ebertmx/SCRAPPY-MK1/src/scrappy_gui.py

import PySimpleGUI as sg
from scrappy_server import *
from serial_reader import *
import traceback
import serial.tools.list_ports
import time

WIN_CLOSED = sg.WIN_CLOSED

STEP = 10

ZERO_POS = "0-position"
ONE_POS = "1-position"
TWO_POS = "2-position"
MAG_STAT = "magnet-status"

ZERO_MOTOR = 0
ONE_MOTOR = 1
TWO_MOTOR = 2

POS = 1
NEG = -1

cmd_list = ["P:0,-350,3000, 50, 30, 50", "P:500,-350,2800, 50, 50, 50","P:500,-550,2900, 50, 30, 30","M:1,0,0,0,0,0","P:-500,-200,2800, 50, 50, 50", "P:-500,-550,2900, 50, 30, 30",  "M:0,0,0,0,0,0","P:0,-350,3000, 50, 50, 50"] # just enter whatever commands you want in this list


class Window(sg.Window):

    def __init__(self):
        super(Window, self).__init__("SCRAPPY-MK1", layout, finalize=True, resizable=True)
        self.serial = None
        self.server = None


def move_0(args, window):
    pass


def move_1(args, window):
    pass


def move_2(args, window):
    pass


def calibrate(args, window):
    pass


def submit(args, window):
    pass


def test(args, window):
    count = 1
    for i in cmd_list:
        window.server.send_command(i)
        if count==1: 
            time.sleep(8)
        if count==2: 
            time.sleep(3)
        if count==3: 
            time.sleep(3)
        if count==4: 
            time.sleep(1)
        if count==5: 
            time.sleep(4)
        if count==6: 
            time.sleep(2)
        if count==7: 
            time.sleep(2)
        if count==8: 
            time.sleep(1)
      
        count=count+1
        


def toggle_mag(args, window):
    state = "0" if args[MAG_STAT] == "1" else "1"
    command = f"M:{state},0,0,0,0,0"
    window[MAG_STAT].update(state)
    window.server.send_command(command)


def start_serial(args, window):
    if window.serial is None:
        window.serial = SerialReader(window)
    window.serial.start(args["port_input"])


def stop_serial(args, window):
    window.serial.stop()


def refresh(args, window):
    print_serial(window)


def clear_cmd_output(args, window):
    window["cmd-output"].update("")


def clear_scrappy_display(args, window):
    window["scrappy-display"].update("")


sg.theme('Dark')
control_column = [
    [sg.Text("Controls", font=("Arial", 20))],
    [sg.HSeparator(pad=(5, (3, 20)))],
    [sg.Text("Motor 0", font=("Arial", 15))],
    [sg.Text("Position"), sg.InputText(size=(10, 10), key=ZERO_POS, default_text="0"), sg.Text("Speed"),
     sg.InputText(size=(10, 10), key="0-speed", default_text="50")],
    [sg.Button("+", size=(5, 1), pad=((5, 40), 3), key="0-forward"),
     sg.Button("-", size=(5, 1), key='0-backward')],
    [sg.HorizontalSeparator(pad=(5, (3, 30)))],
    [sg.Text("Motor B", font=("Arial", 15))],
    [sg.Text("Position"), sg.InputText(size=(10, 10), key=ONE_POS, default_text="0"), sg.Text("Speed"),
     sg.InputText(size=(10, 10), key="1-speed", default_text="50")],
    [sg.Button("+", size=(5, 1), pad=((5, 40), 3), key="1-forward"),
     sg.Button("-", size=(5, 1), key='1-backward')],
    [sg.HorizontalSeparator(pad=(5, (3, 30)))],
    [sg.Text("Motor C", font=("Arial", 15))],
    [sg.Text("Position"), sg.InputText(size=(10, 10), key=TWO_POS, default_text="0"), sg.Text("Speed"),
     sg.InputText(size=(10, 10), key="2-speed", default_text="50")],
    [sg.Button("+", size=(5, 1), pad=((5, 40), 3), key="2-forward"),
     sg.Button("-", size=(5, 1), key='2-backward')],
    [sg.HorizontalSeparator(pad=(5, (3, 30)))],
    [sg.Text("Magnet", font=("Arial", 15))],
    [sg.Text("Status"), sg.InputText(size=(10, 10), key=MAG_STAT, default_text="0"),
     sg.Button("Toggle", size=(5, 1), pad=((5, 40), 3), key=toggle_mag)],
    [sg.HorizontalSeparator(pad=(5, (3, 30)))],
    [sg.Button("Submit", size=(10, 3), key="motor-submit"), sg.Button("Calibrate", size=(10, 3), key="calibrate"),
     sg.Button("Test", size=(10, 3), key=test)],
    [sg.HorizontalSeparator(pad=(5, (3, 30)))],
    [sg.Text("Command Output", font=("Arial", 20))],
    [sg.Multiline(size=(43, 15), key='cmd-output', background_color='black', text_color='green', reroute_stdout=False,
                  autoscroll=True)],
    [sg.InputText(key='cmd-input', size=(38, 3), do_not_clear=False), sg.Button("Clear", key=clear_cmd_output)]
]
data_column = [
    [sg.Text("SCRAPPY Output", font=("Arial", 20))],
    [sg.Multiline(size=(40, 49), key='scrappy-display', background_color='black', text_color='green',
                  reroute_stdout=False, reroute_stderr=True, autoscroll=True)],
    [sg.Button("Clear", key=clear_scrappy_display)]
]

network_column = [
    [sg.Text("Network", font=("Arial", 20))],
    [sg.Text(size=(43, 15), key='network-display', background_color='black', text_color='green')],
    [sg.Button("Reconnect", size=(15, 3), pad=((5, 46), (1, 50)), key="connect"),
     sg.Button("Disconnect", size=(15, 3), pad=((46, 5), (1, 50)), key='disconnect')],
    [sg.Text("Serial", font=("Arial", 20))],
    [sg.Text(size=(43, 15), key='serial-display', background_color='black', text_color='green')],
    [sg.Text("Port:"), sg.InputText(key='port_input', size=(35, 3)), sg.Button("Refresh", size=(5, 1), key=refresh)],
    [sg.Button("Start Serial", size=(15, 3), pad=((5, 46), (1, 50)), key=start_serial),
     sg.Button("Stop Serial", size=(15, 3), pad=((46, 5), (1, 50)), key=stop_serial)],

]

layout = [
    [
        sg.Column(control_column, justification='left', vertical_alignment='top'),
        sg.Column(network_column, vertical_alignment='top'),
        sg.Column(data_column, vertical_alignment='top')
    ]
]


def print_serial(window):
    default_serial_string = \
        f"""Serial Port: None
Connected: False
Available Ports:
"""
    for i in serial.tools.list_ports.comports():
        default_serial_string += f"    {i.name} - {i.description}\n"

    window['serial-display'].update(default_serial_string)


def setup_window(window, server):
    window.maximize()
    window['cmd-input'].bind("<Return>", "_Enter")
    window.server = server
    server.print_network_status()
    print_serial(window)


def send_move_command(command, values, server):
    command = f"{command}:{values['0-position']},{values['1-position']},{values['2-position']},{values['0-speed']},{values['1-speed']},{values['2-speed']}"
    if ",," in command or len(values['0-position']) == 0 or len(values["2-speed"]) == 0:
        server.print_to_element(f"Invalid move arguments {command}", "cmd-output")
        return False
    server.send_command(command)
    return True


def handle_event(event, values, window):
    server = window.server
    if callable(event):
        event(values, window)
    elif event == "serial-event":
        server.send_command(values['serial-event'])
    elif event == "cmd-input_Enter":
        server.send_command(values['cmd-input'])
    elif event == 'connect':
        server.start()
    elif event == 'disconnect':
        server.disconnect()
    elif event == "calibrate":
        server.arm_calibrated = send_move_command("C", values, server)
    elif event == 'motor-submit':
        if not server.arm_calibrated:
            server.print_to_element("Not calibrated", "cmd-output")
            return
        send_move_command("P", values, server)
    elif event == "test":
        command = "P:100,100,100,30,30,30"
        server.send_command(command)
    elif "-forward" in event or "-backward" in event:
        zero_pos = int(values['0-position'])
        one_pos = int(values['1-position'])
        two_pos = int(values['2-position'])
        if "0-" in event:
            values['0-position'] = str(zero_pos + STEP if "forward" in event else zero_pos - STEP)
            window[ZERO_POS].update(values['0-position'])
        elif "1-" in event:
            values['1-position'] = str(one_pos + STEP if "forward" in event else one_pos - STEP)
            window[ONE_POS].update(values['1-position'])
        elif "2-" in event:
            values['2-position'] = str(two_pos + STEP if "forward" in event else two_pos - STEP)
            window[TWO_POS].update(values['2-position'])
        send_move_command("P", values, server)


def main():
    window = Window()
    with ArmServer(ADDRESS, window) as server:
        setup_window(window, server)
        server.start()
        while True:
            event, values = window.read()
            if event == WIN_CLOSED:
                break
            try:
                handle_event(event, values, window)
            except Exception as e:
                print(e)
                traceback.print_exc()
            server.print_network_status()

        window.close()


if __name__ == '__main__':
    main()
